sercan-gundogdu/kumand/source/firmware/esp8266/main/main.h

// ----------------------------------------------------------------------------
//
//
// ----------------------------------------------------------------------------
#ifdef __cplusplus
  #include <ESP8266WiFi.h>
  extern "C" {
#endif

// ----------------------------------------------------------------------------
#include <stdint.h>
#include "gpio.h"
#include "user_interface.h"
#include "ioctl.h"
#include "cmdctl.h"
#include "netctl.h"
#include "pwrctl.h"

#ifdef __cplusplus
  }
#endif
