sercan-gundogdu/kumand/source/firmware/esp8266/main/cmdctl.h

// ----------------------------------------------------------------------------
//
//
// ----------------------------------------------------------------------------
#ifdef __cplusplus
  extern "C" {
#endif

// ----------------------------------------------------------------------------
#include <stdint.h>

// ----------------------------------------------------------------------------
void cmdctl_init();

// ----------------------------------------------------------------------------
void cmdctl_loop();

#ifdef __cplusplus
  }
#endif
