sercan-gundogdu/kumand/source/firmware/esp8266/main/ioctl.h

// ----------------------------------------------------------------------------
//
//
// ----------------------------------------------------------------------------
#ifdef __cplusplus
  extern "C" {
#endif

// ----------------------------------------------------------------------------
#include <stdint.h>

// ----------------------------------------------------------------------------
#define IO_PIN_SIG_WAKE     14
#define IO_PIN_LED_RED      13
#define IO_PIN_LED_GREEN    12

// ----------------------------------------------------------------------------
void ioctl_init();

// ----------------------------------------------------------------------------
void ioctl_led_on(uint8_t l_io_pin_num);

// ----------------------------------------------------------------------------
void ioctl_led_off(uint8_t l_io_pin_num);

// ----------------------------------------------------------------------------
void ioctl_led_blink_pattern_1(uint8_t l_io_pin_num, uint8_t l_io_delay_ms);

// ----------------------------------------------------------------------------
void ioctl_led_blink_pattern_2(
  uint8_t l_io_pin_1_num, uint8_t l_io_pin_2_num, uint8_t l_io_delay_ms
);

#ifdef __cplusplus
  }
#endif
