sercan-gundogdu/kumand/source/firmware/esp8266/main/netctl.h

// ----------------------------------------------------------------------------
//
//
// ----------------------------------------------------------------------------
#ifdef __cplusplus
  extern "C" {
#endif

// ----------------------------------------------------------------------------
#include <stdint.h>

// ----------------------------------------------------------------------------
void netctl_init();

// ----------------------------------------------------------------------------
void netctl_host_set(String l_host);

// ----------------------------------------------------------------------------
void netctl_port_set(String l_port);

// ----------------------------------------------------------------------------
void netctl_wifi_reconnect();

// ----------------------------------------------------------------------------
void netctl_wifi_wps_run();

// ----------------------------------------------------------------------------
void netctl_tcp_send();

// ----------------------------------------------------------------------------
void netctl_dest_address_get();

#ifdef __cplusplus
  }
#endif
